neilkatahira/EE-Emerge-2020-Loopmaster/pictures/Camera and Hub.jpg

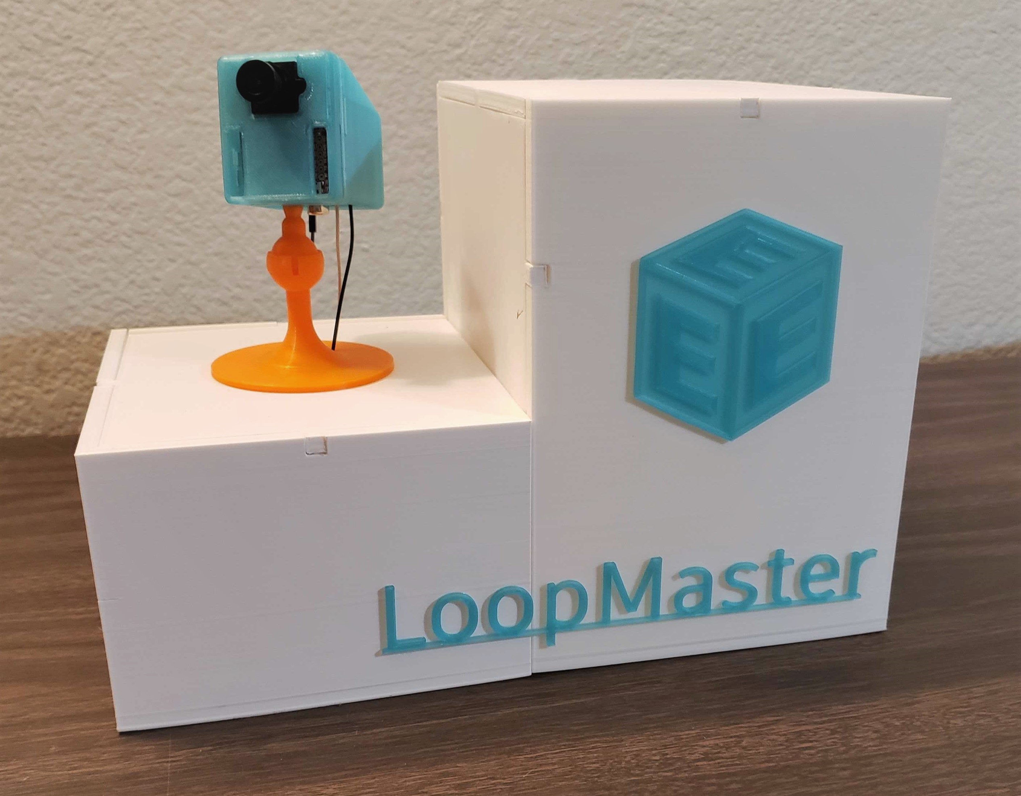
pictures/Camera and Hub.jpg
